svenpetersen1965/C64-PSU-Global/Case/Rev 0/pictures/C64PSU_Global_2020-Feb-03_11-47-49AM-000_CustomizedView1905755716.png

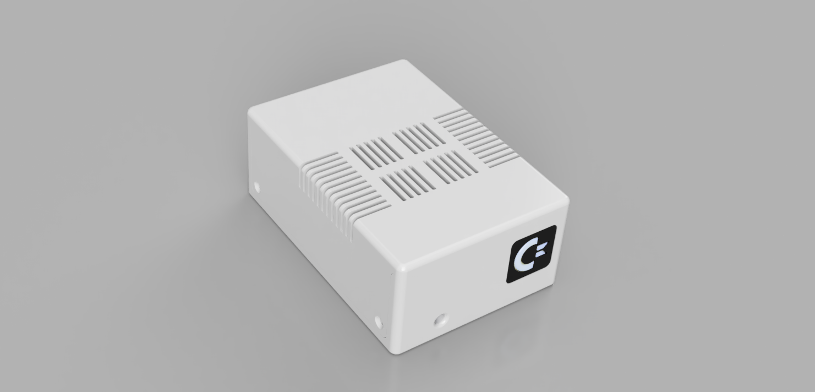
Case/Rev 0/pictures/C64PSU_Global_2020-Feb-03_11-47-49AM-000_CustomizedView1905755716.png
