svenpetersen1965/C64-PSU-Global/Case/Rev 0/pictures/C64PSU_Global_2020-Jan-24_03-44-14PM-000_CustomizedView20103797462.png

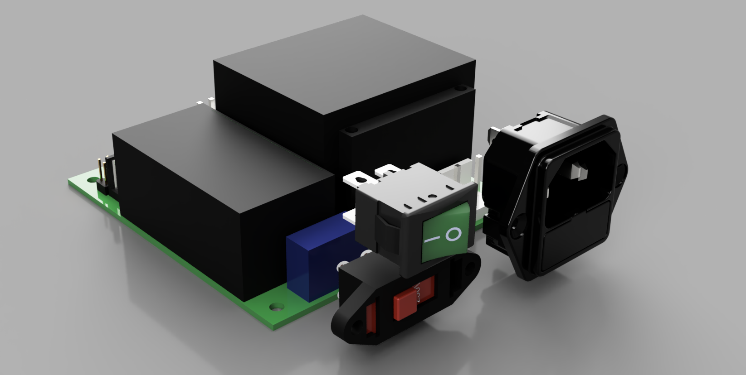
Case/Rev 0/pictures/C64PSU_Global_2020-Jan-24_03-44-14PM-000_CustomizedView20103797462.png
