svenpetersen1965/C64-PSU-Global/Case/Rev 0/pictures/C64PSU_Global_2020-Jan-25_06-23-07PM-000_CustomizedView7411572082.jpg

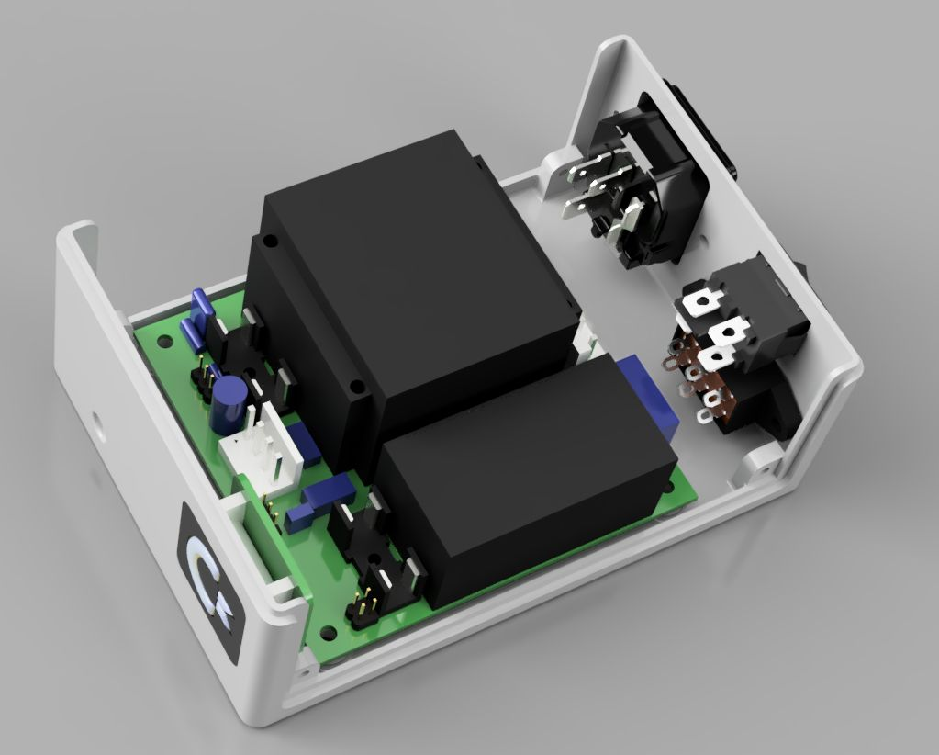
Case/Rev 0/pictures/C64PSU_Global_2020-Jan-25_06-23-07PM-000_CustomizedView7411572082.jpg
