svenpetersen1965/C64-PSU-Global/Case/Rev 0/pictures/C64PSU_Global_2020-Jan-25_08-59-41PM-000_CustomizedView21250095987.jpg

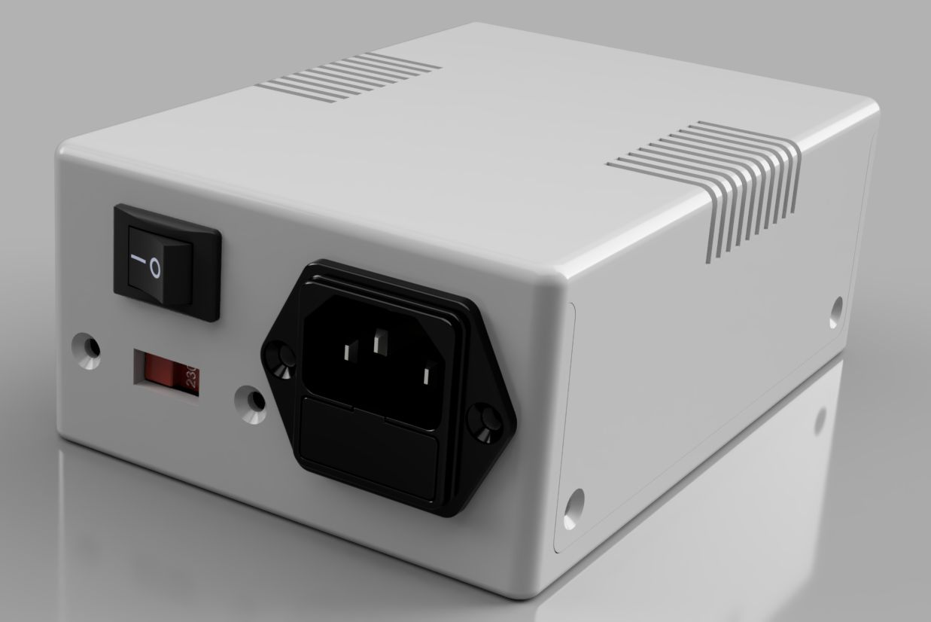
Case/Rev 0/pictures/C64PSU_Global_2020-Jan-25_08-59-41PM-000_CustomizedView21250095987.jpg
