svenpetersen1965/C64-PSU-Global/Case/Rev 0/pictures/C64PSU_Global_2020-Jan-25_12-00-59PM-000_CustomizedView4116816318.jpg

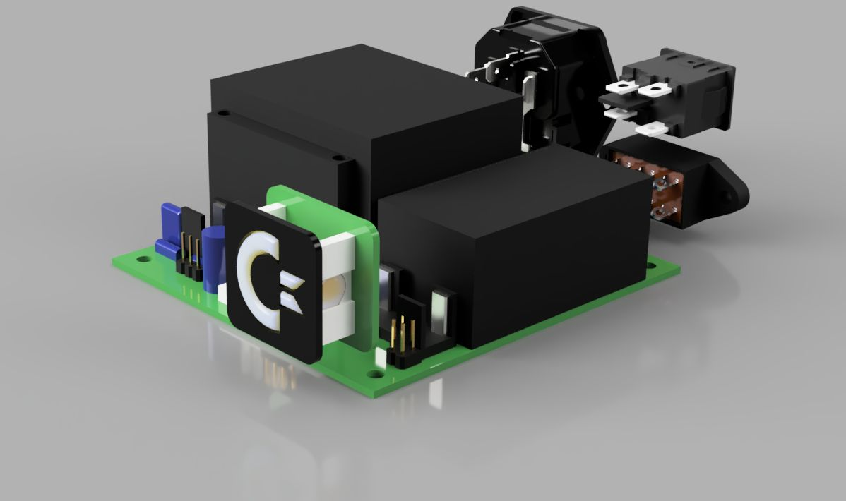
Case/Rev 0/pictures/C64PSU_Global_2020-Jan-25_12-00-59PM-000_CustomizedView4116816318.jpg
