svenpetersen1965/C64-PSU-Global/Rev. 1/Inkscape/C64_PSU_230_115.png

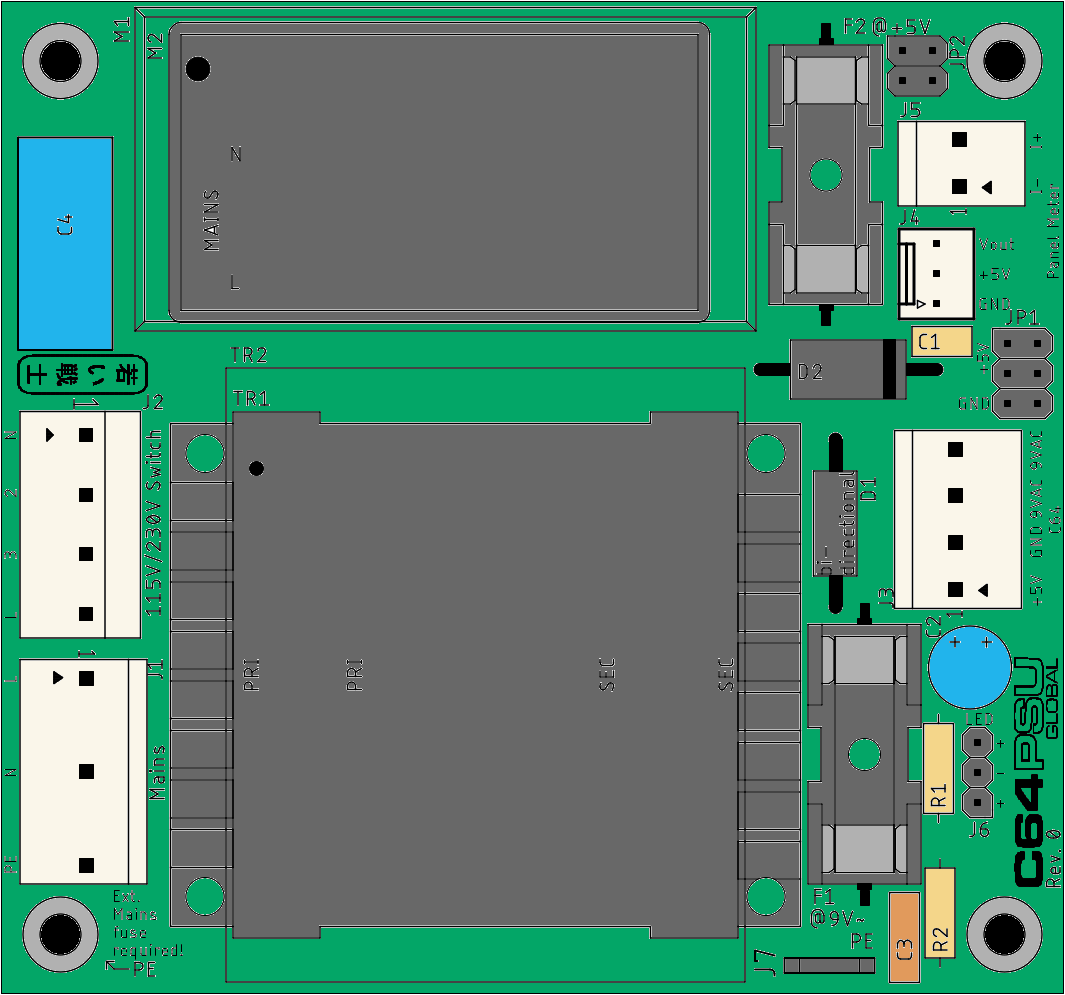
Rev. 1/Inkscape/C64_PSU_230_115.png
