svenpetersen1965/C64-PSU-Global/Rev. 1/pictures/3654_psu_glob_both.JPG

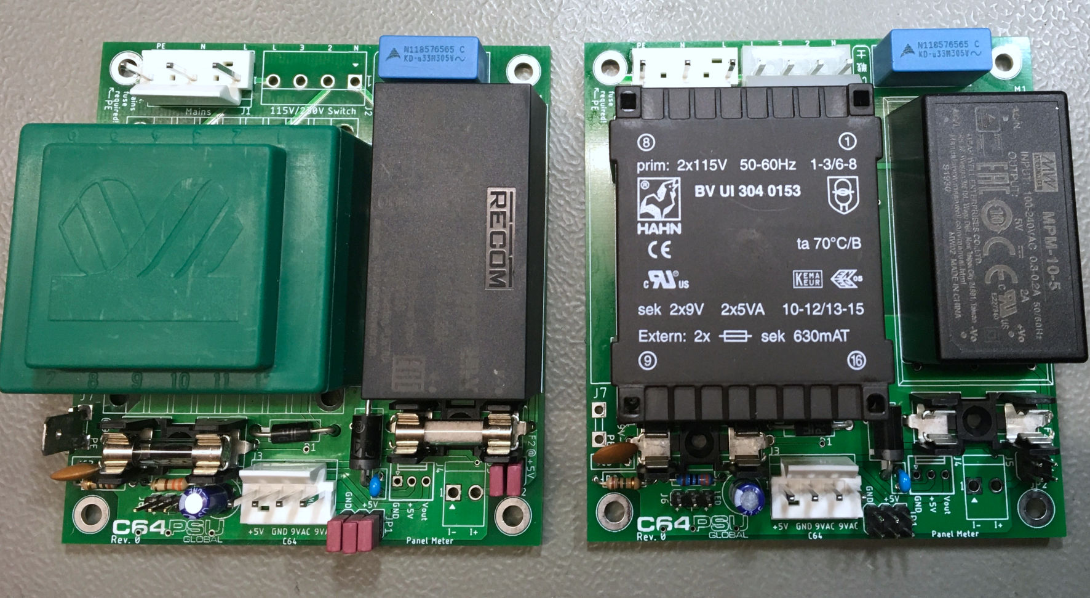
Rev. 1/pictures/3654_psu_glob_both.JPG
