svenpetersen1965/C64-PSU-Global/Rev. 1/pictures/3697_wired_rev0.JPG

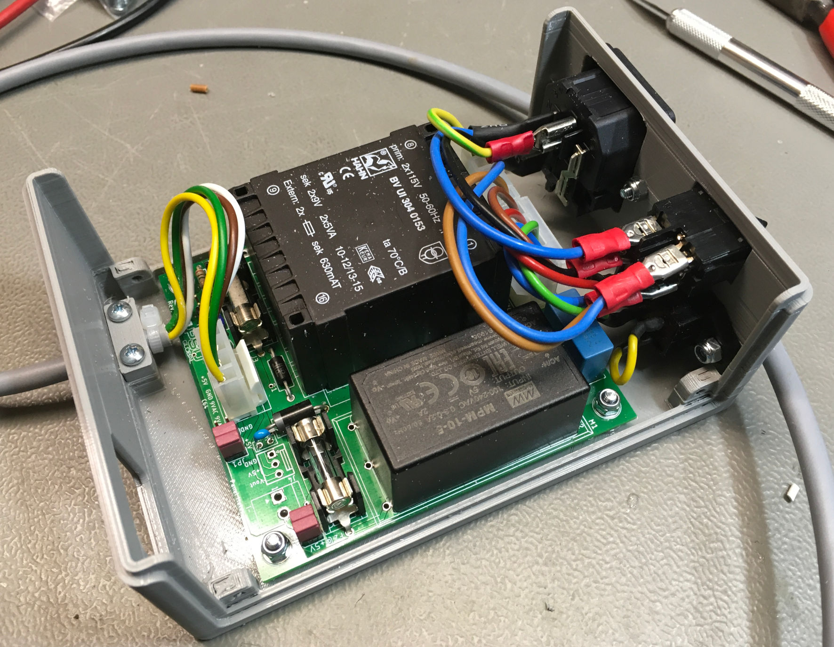
Rev. 1/pictures/3697_wired_rev0.JPG
