svenpetersen1965/C64-PSU-Global/Rev. 1/pictures/3714-mains_cable_inlet.JPG

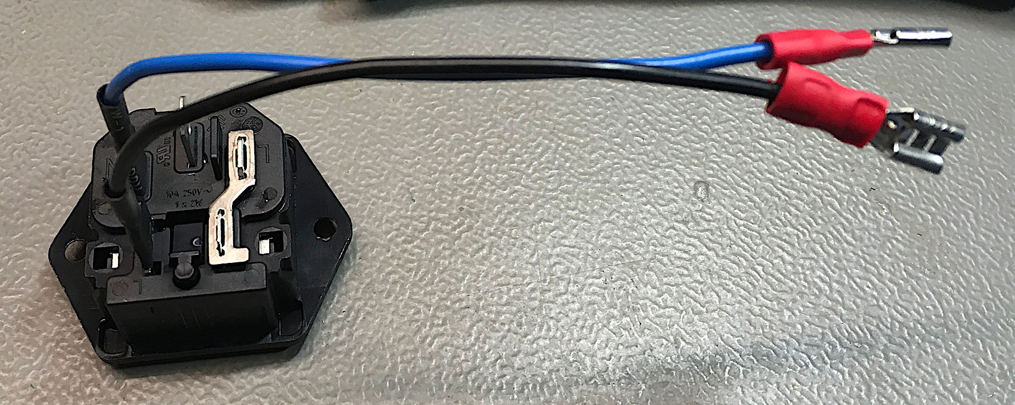
Rev. 1/pictures/3714-mains_cable_inlet.JPG
