svenpetersen1965/C64-PSU-Global/Rev. 1/pictures/3715_appliance_connector_wired.JPG

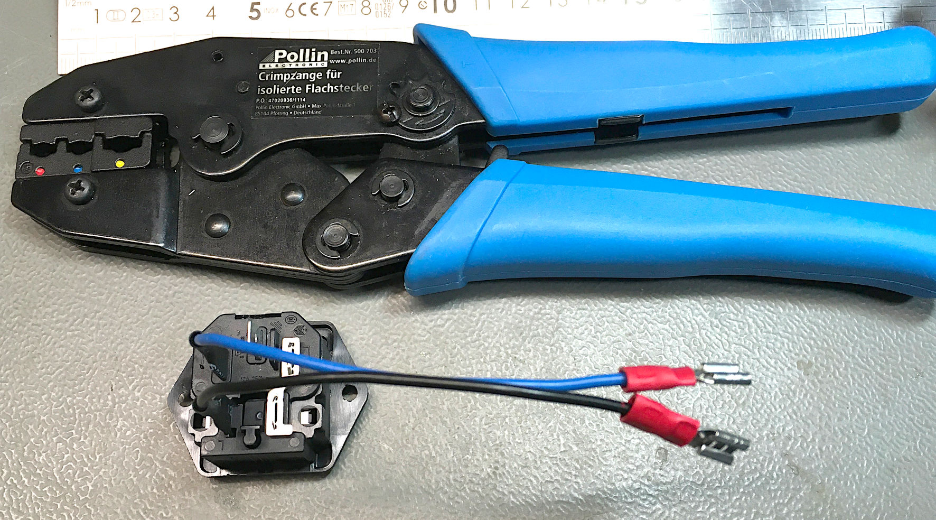
Rev. 1/pictures/3715_appliance_connector_wired.JPG
