svenpetersen1965/C64-PSU-Global/Rev. 1/pictures/3716_power_cable_j1.JPG

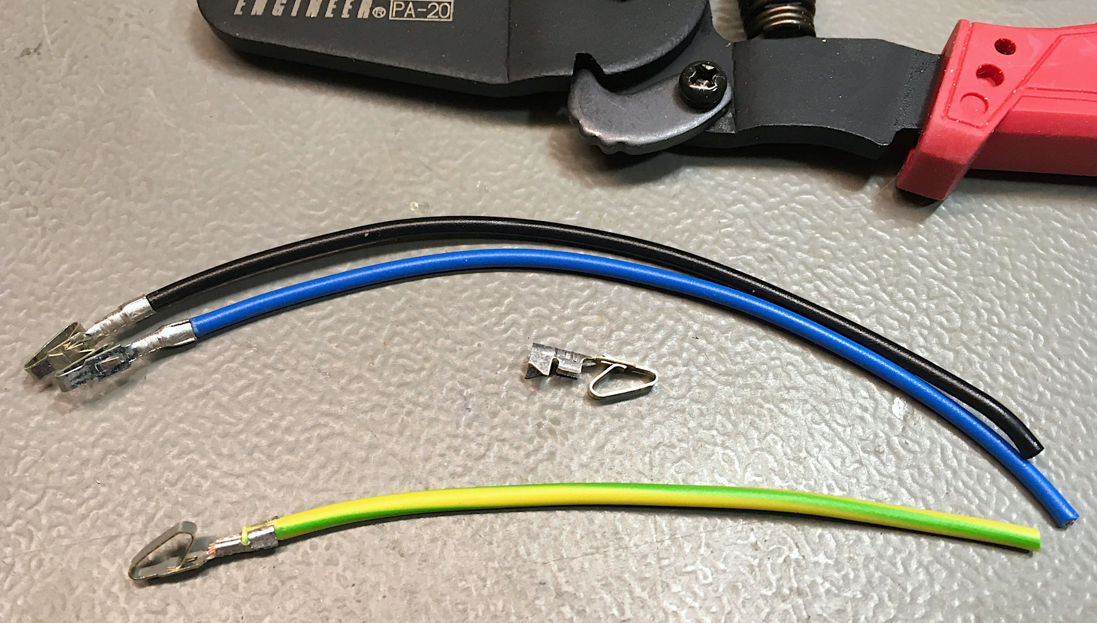
Rev. 1/pictures/3716_power_cable_j1.JPG
