svenpetersen1965/C64-PSU-Global/Rev. 1/pictures/3717_mains_cable.JPG

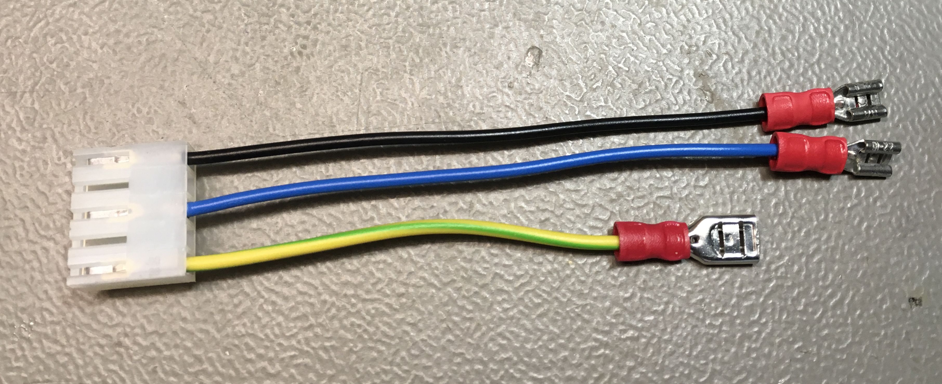
Rev. 1/pictures/3717_mains_cable.JPG
