svenpetersen1965/C64-PSU-Global/Rev. 1/pictures/3718_voltage_selector.JPG

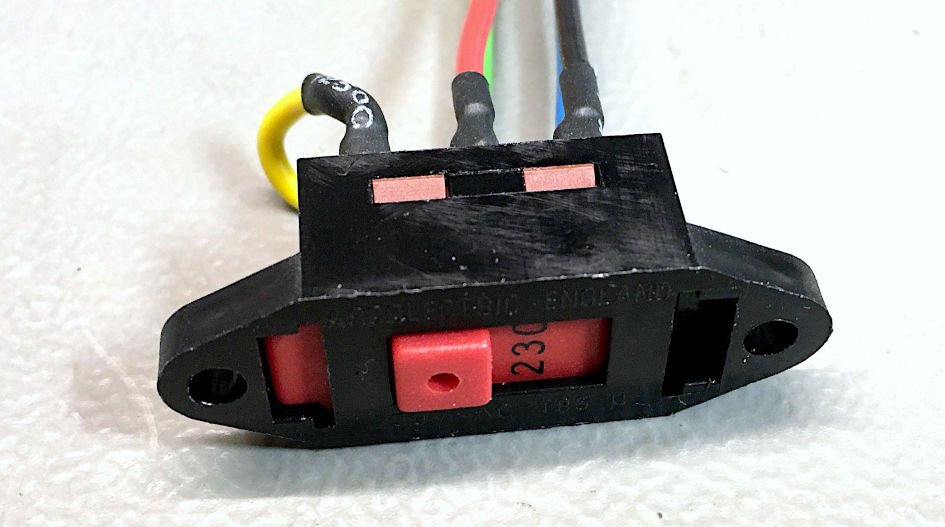
Rev. 1/pictures/3718_voltage_selector.JPG
