svenpetersen1965/C64-PSU-Global/Rev. 1/pictures/3720_voltage_selector_crimped.JPG

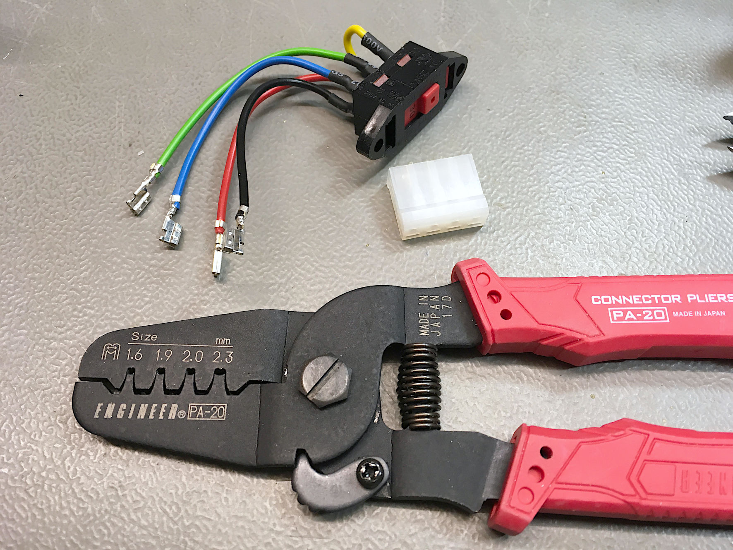
Rev. 1/pictures/3720_voltage_selector_crimped.JPG
