svenpetersen1965/C64-PSU-Global/Rev. 1/pictures/3721_voltage_selector_w300.JPG

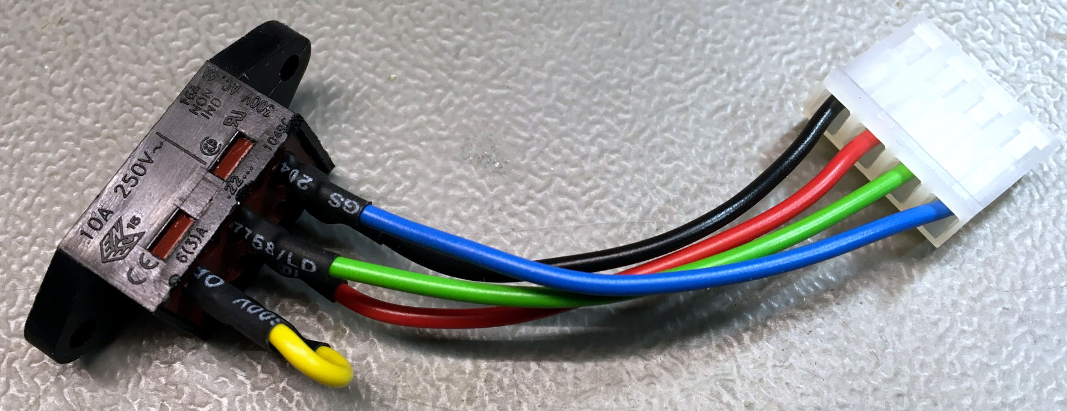
Rev. 1/pictures/3721_voltage_selector_w300.JPG
