svenpetersen1965/C64-PSU-Global/Rev. 1/pictures/3726_mains_switch.JPG

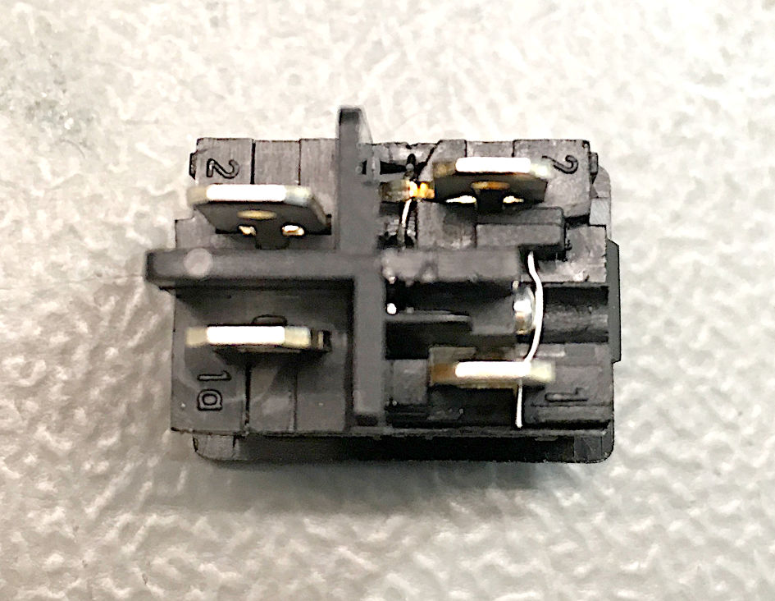
Rev. 1/pictures/3726_mains_switch.JPG
