svenpetersen1965/C64-PSU-Global/Rev. 1/pictures/3728_mains_switch_connected.JPG

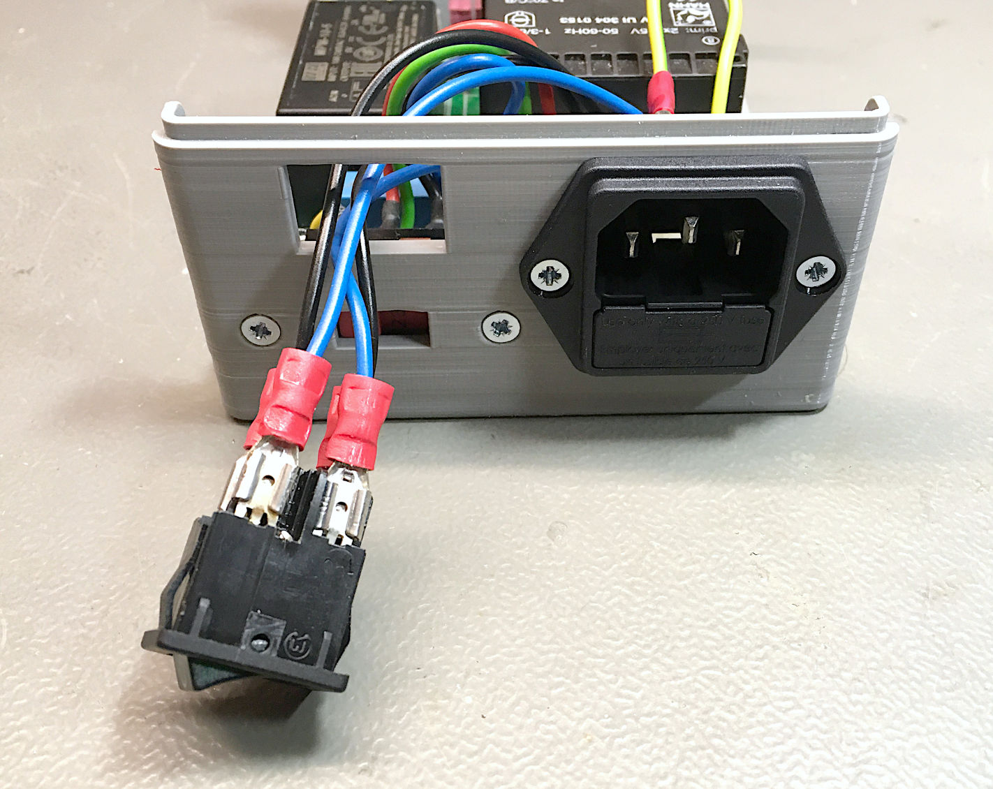
Rev. 1/pictures/3728_mains_switch_connected.JPG
