svenpetersen1965/C64-PSU-Global/Rev. 1/pictures/3742_dim_power_switch_115V.JPG

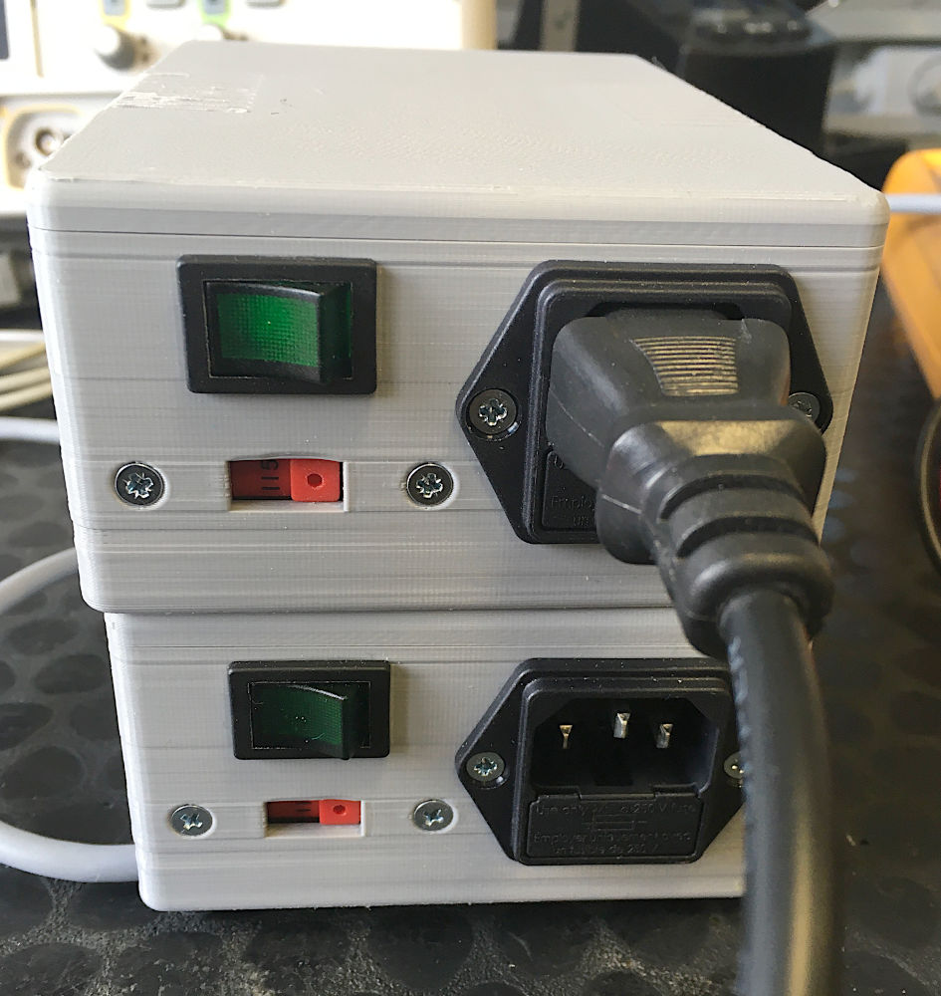
Rev. 1/pictures/3742_dim_power_switch_115V.JPG
