svenpetersen1965/C64-PSU-Global/Rev. 1/pictures/3744_din_connector_output_cable.JPG

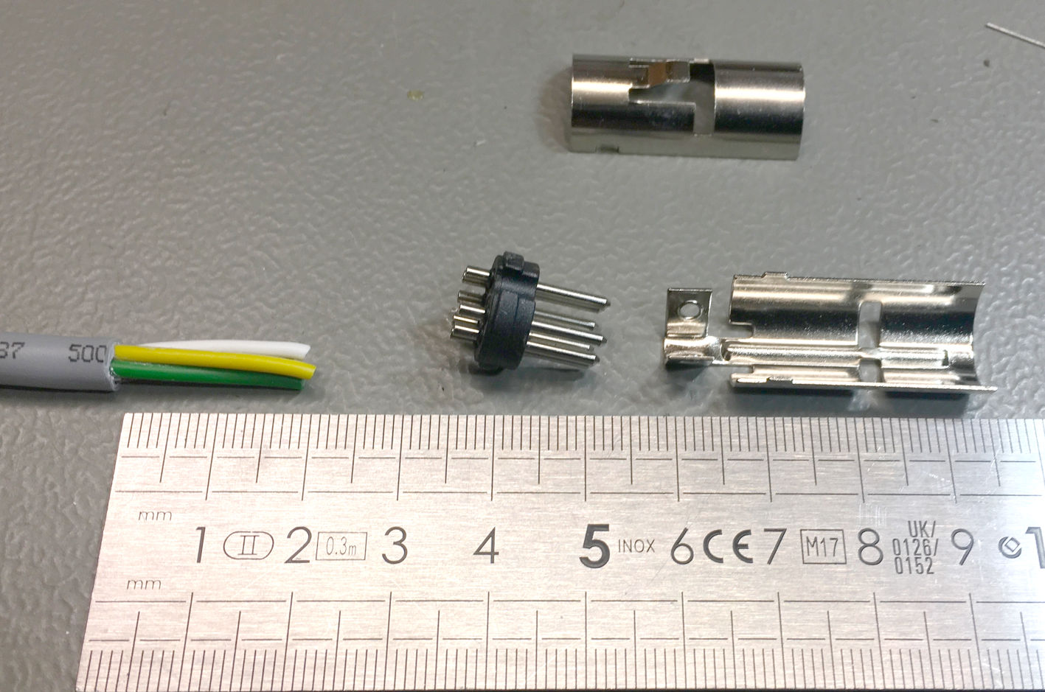
Rev. 1/pictures/3744_din_connector_output_cable.JPG
