svenpetersen1965/C64-PSU-Global/Rev. 1/pictures/3749_din_connector_shield.JPG

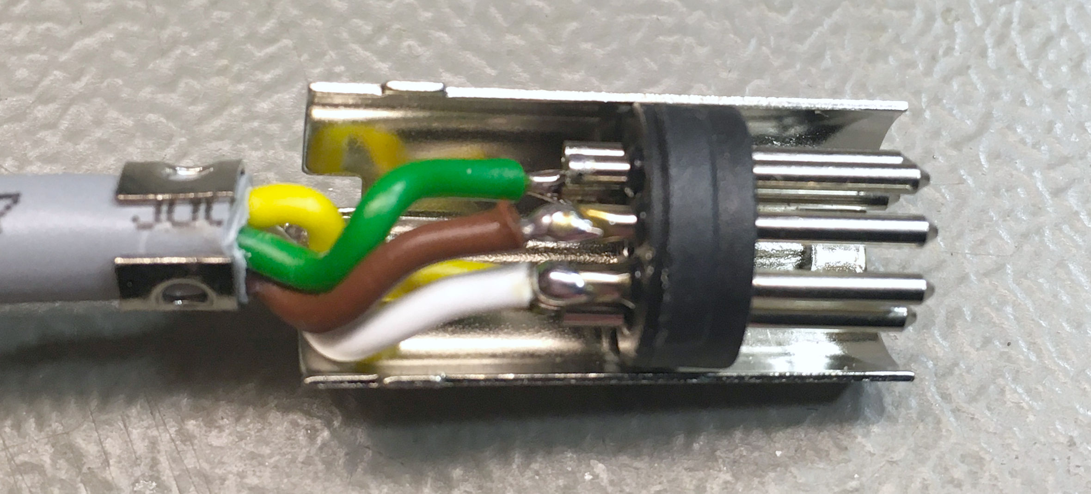
Rev. 1/pictures/3749_din_connector_shield.JPG
