svenpetersen1965/C64-PSU-Global/Rev. 1/pictures/3751_rev0_230V_only.JPG

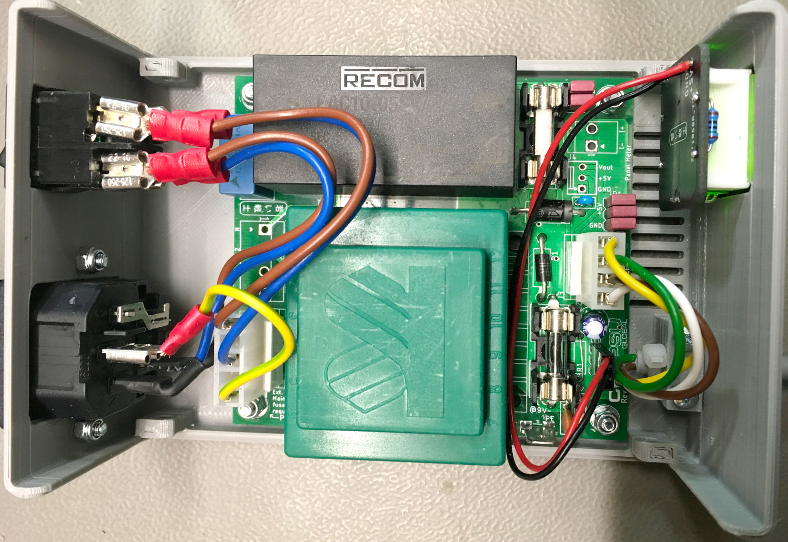
Rev. 1/pictures/3751_rev0_230V_only.JPG
