svenpetersen1965/C64-PSU-Global/Rev. 1/pictures/3837_thermal_resistor_load_initial.JPG

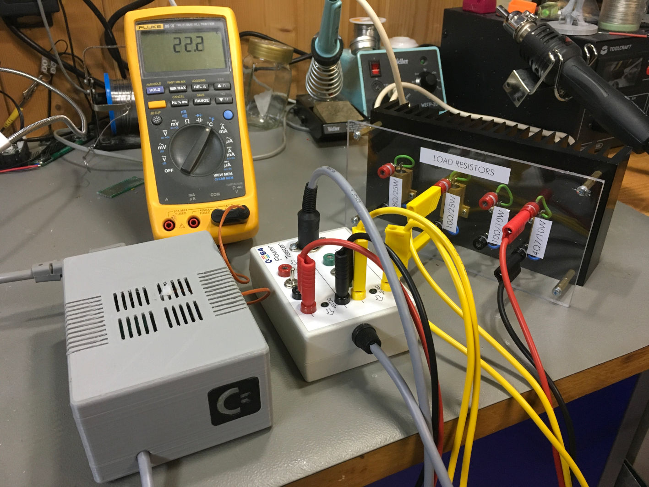
Rev. 1/pictures/3837_thermal_resistor_load_initial.JPG
