svenpetersen1965/C64-PSU-Global/Rev. 1/pictures/3838_thermal_resistor_load_0_28h.JPG

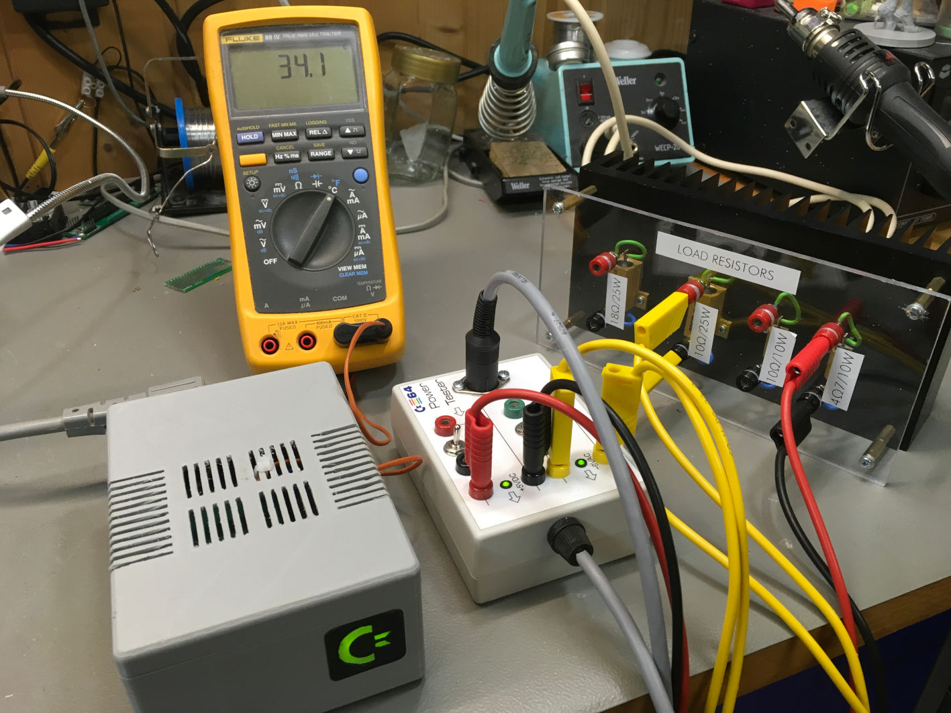
Rev. 1/pictures/3838_thermal_resistor_load_0_28h.JPG
