svenpetersen1965/C64-PSU-Global/Rev. 1/pictures/3839_thermal_resistor_load_02_16h.JPG

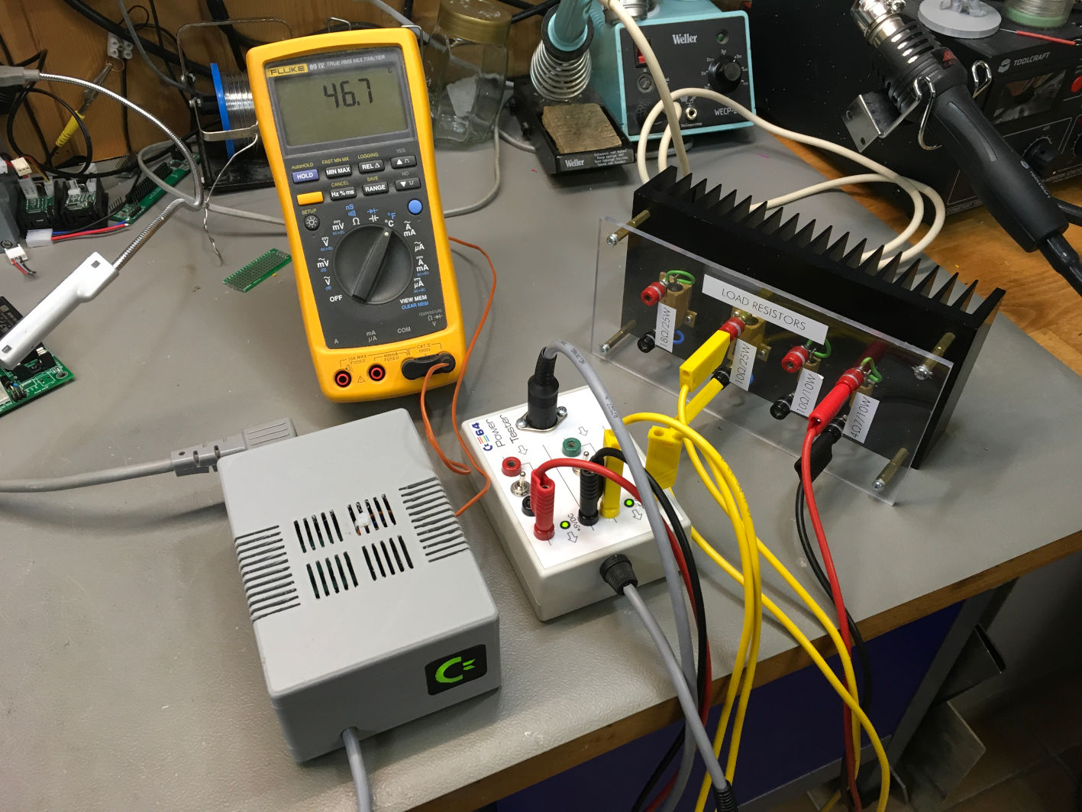
Rev. 1/pictures/3839_thermal_resistor_load_02_16h.JPG
