svenpetersen1965/C64-PSU-Global/Rev. 1/pictures/3840_final_temperature_resistor_load.JPG

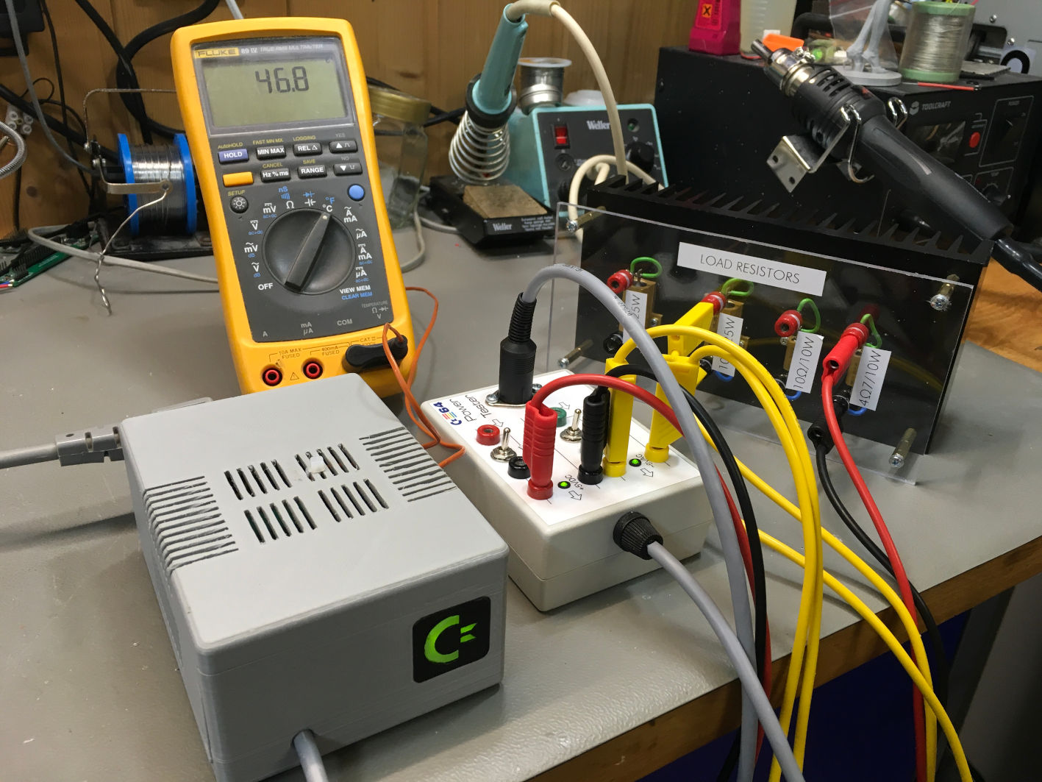
Rev. 1/pictures/3840_final_temperature_resistor_load.JPG
