svenpetersen1965/C64-PSU-Global/Rev. 1/pictures/3842_thermal_RLT_initial.JPG

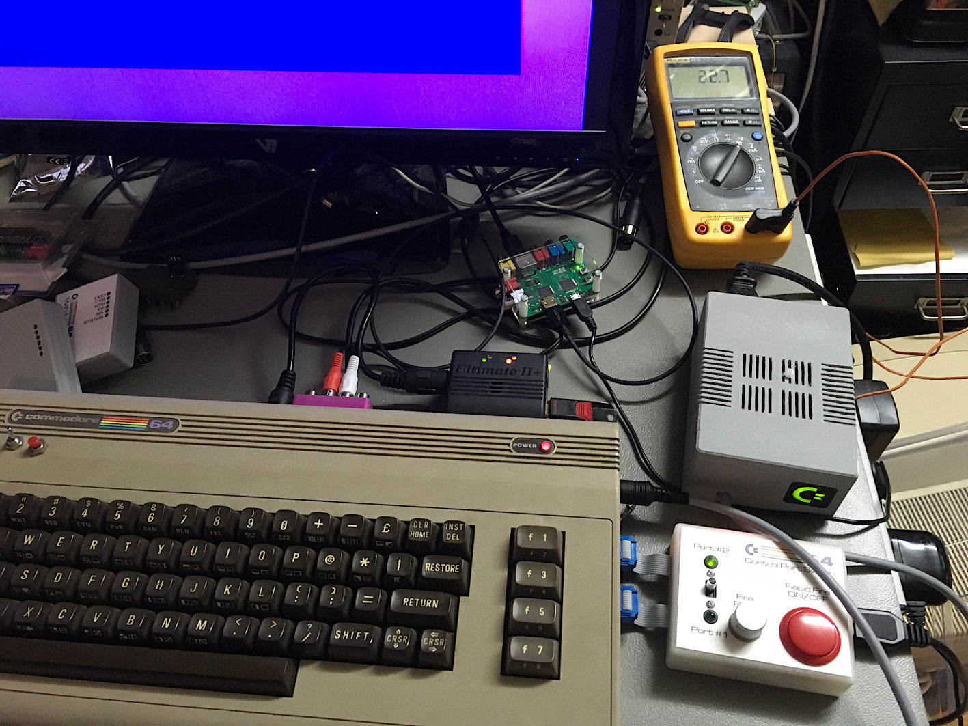
Rev. 1/pictures/3842_thermal_RLT_initial.JPG
