svenpetersen1965/C64-PSU-Global/Rev. 1/pictures/3843_thermal_RLT_0_00h.JPG

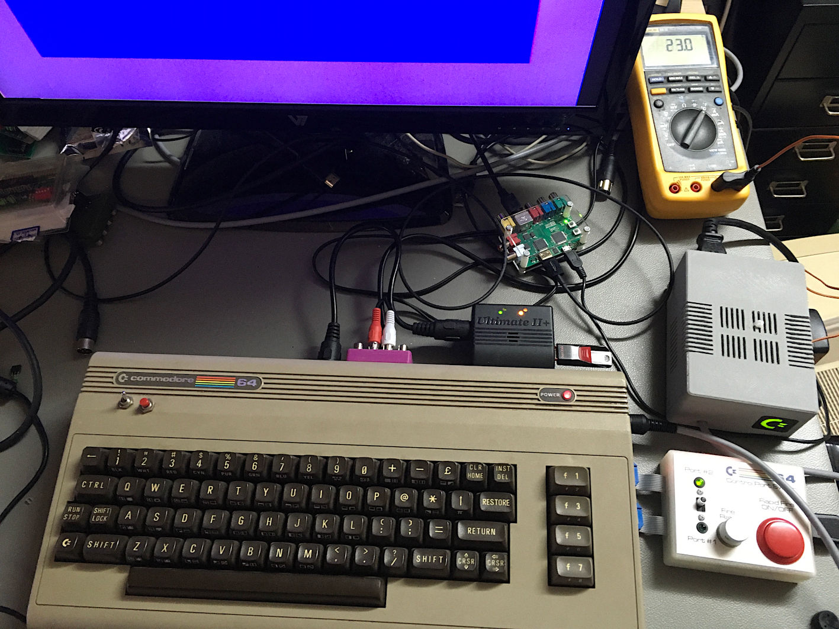
Rev. 1/pictures/3843_thermal_RLT_0_00h.JPG
