svenpetersen1965/C64-PSU-Global/Rev. 1/pictures/3845_thermal_RLT_0_54h.JPG

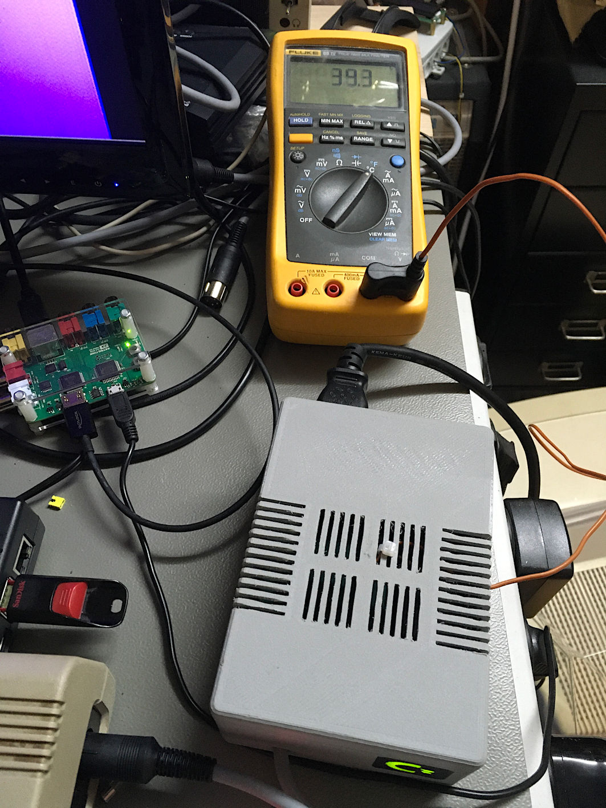
Rev. 1/pictures/3845_thermal_RLT_0_54h.JPG
