svenpetersen1965/C64-PSU-Global/Rev. 1/pictures/3846_thermal_RLT_1_49h.JPG

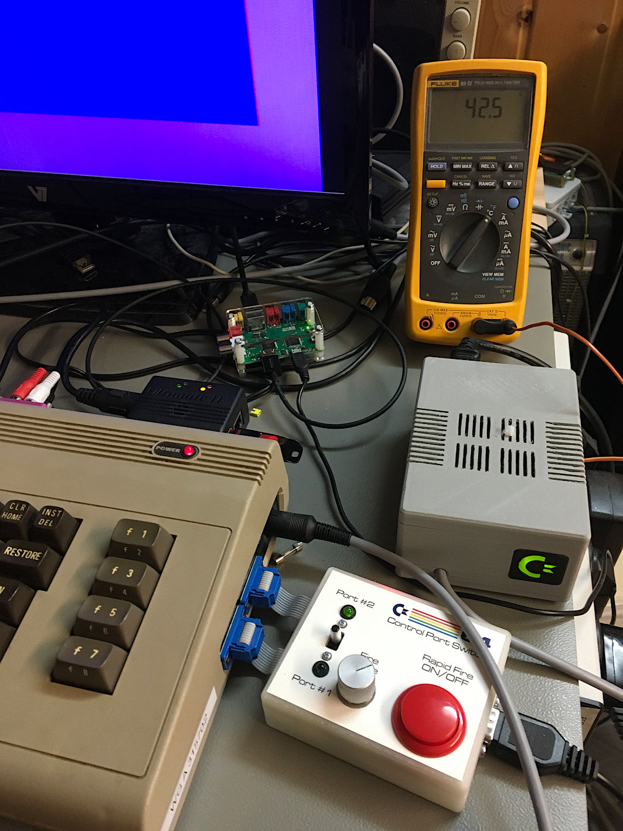
Rev. 1/pictures/3846_thermal_RLT_1_49h.JPG
