svenpetersen1965/C64-PSU-Global/Rev. 1/pictures/3847_thermal_RLT_2_29h.JPG

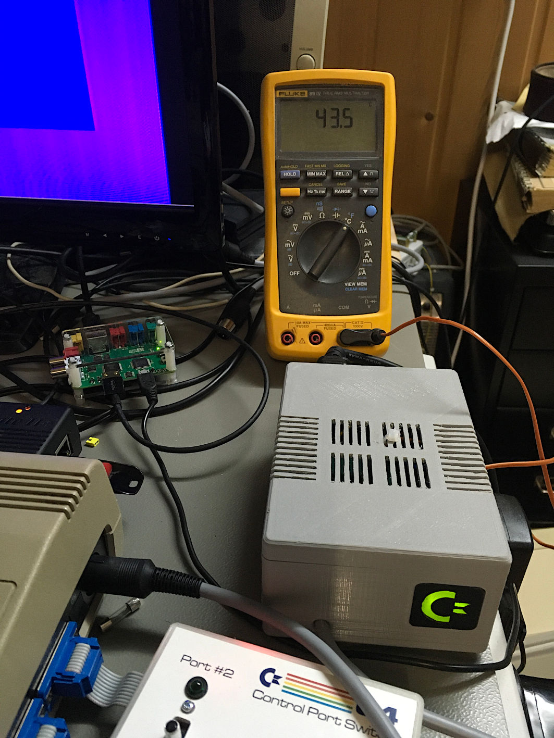
Rev. 1/pictures/3847_thermal_RLT_2_29h.JPG
