svenpetersen1965/C64-PSU-Global/Rev. 1/pictures/4185_c64_PSU_global_Rev_1.JPG

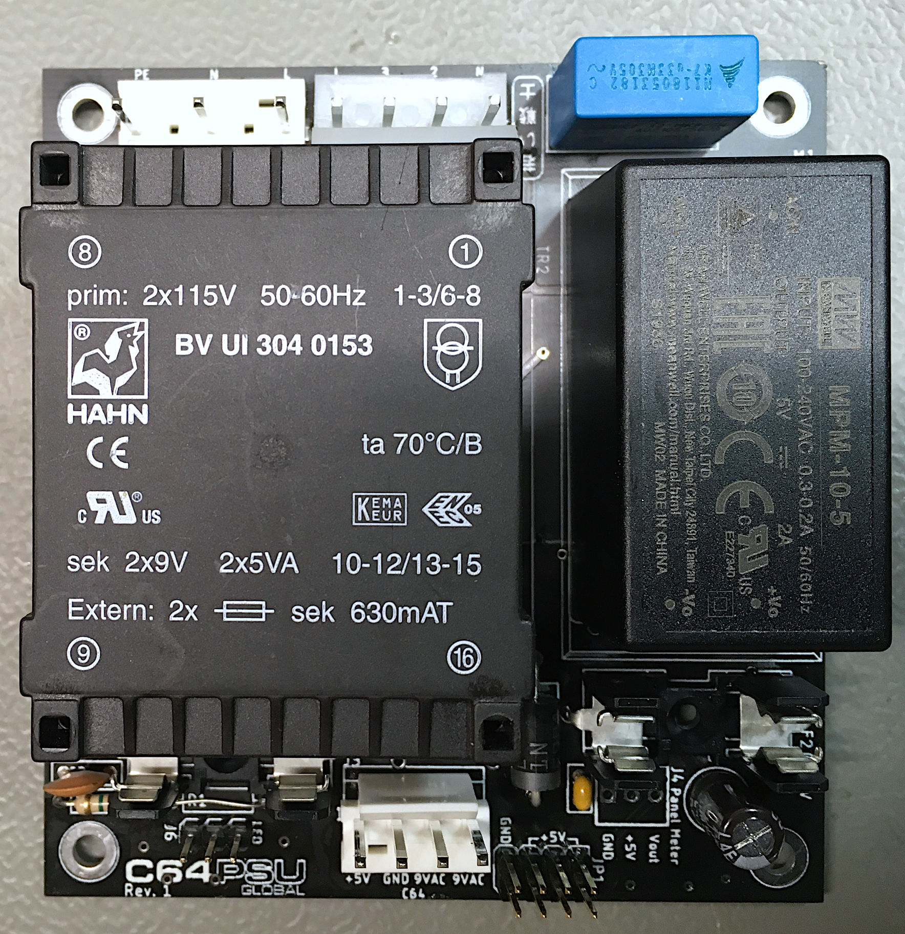
Rev. 1/pictures/4185_c64_PSU_global_Rev_1.JPG
