svenpetersen1965/C64-PSU-Global/Rev. 1/pictures/4326_screws.xnbak.jpg

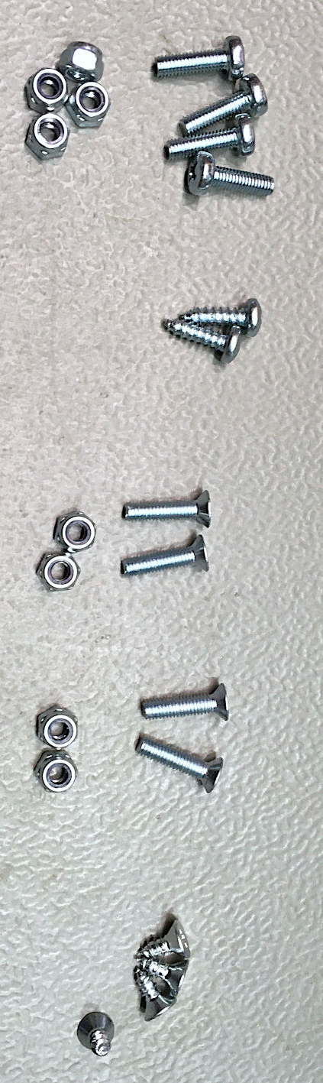
Rev. 1/pictures/4326_screws.xnbak.jpg
