svenpetersen1965/C64-PSU-Global/Rev. 1/pictures/4329_rev1_wired.JPG

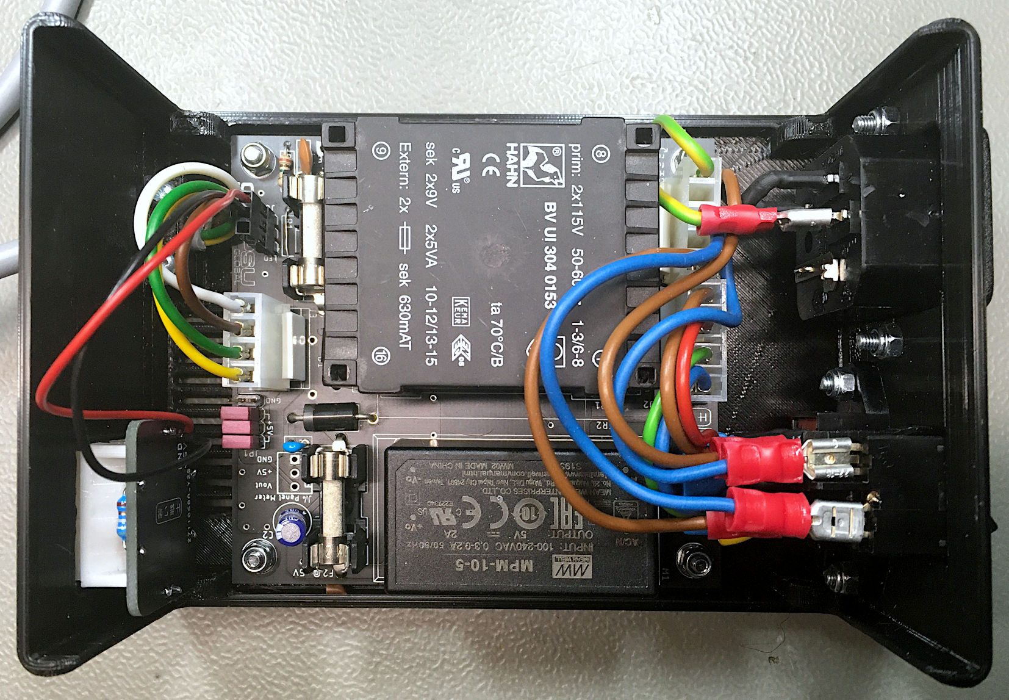
Rev. 1/pictures/4329_rev1_wired.JPG
