svenpetersen1965/C64-PSU-Global/Rev. 1/pictures/block diagram.png

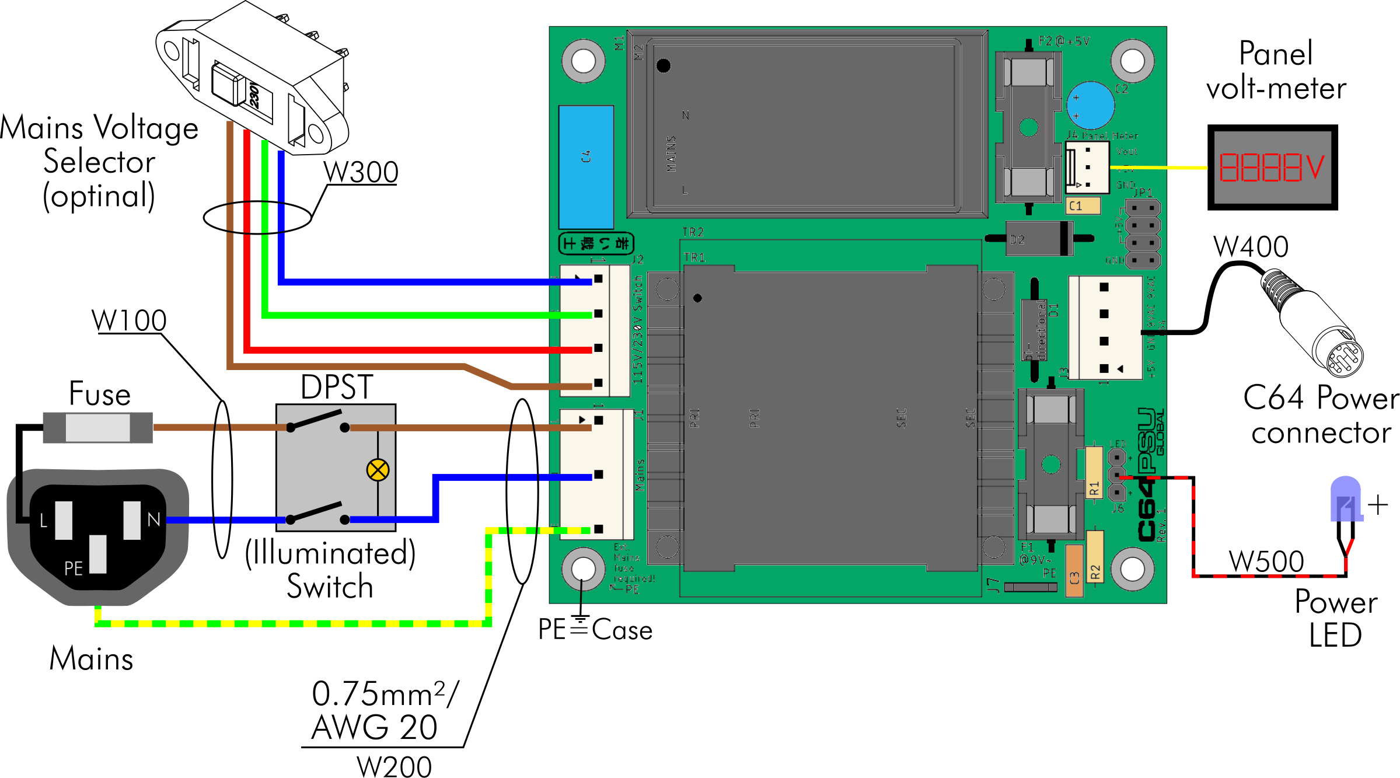
Rev. 1/pictures/block diagram.png
