svenpetersen1965/C64-PSU-Global/Rev. 1/pictures/mains_voltage_selector.png

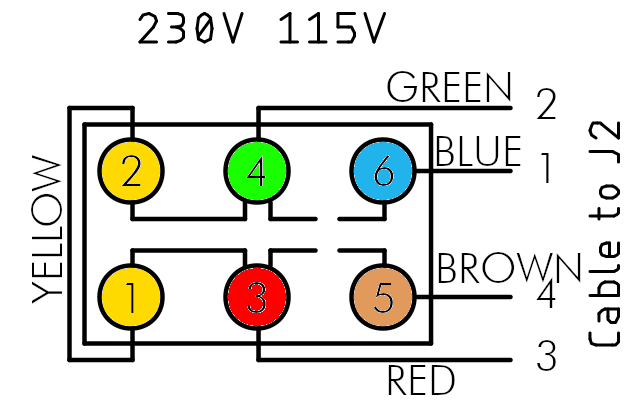
Rev. 1/pictures/mains_voltage_selector.png
