svenpetersen1965/C64-PSU-Global/Rev. 1/pictures/PSU_Global_case_2_bottoms.jpg

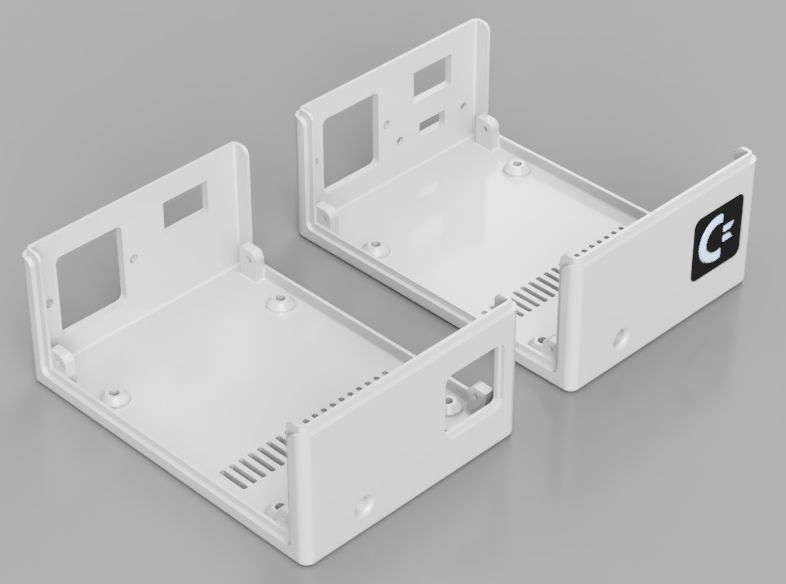
Rev. 1/pictures/PSU_Global_case_2_bottoms.jpg
