svenpetersen1965/C64-PSU-Global/Rev. 1/pictures/3711_installing_output_cable.JPG

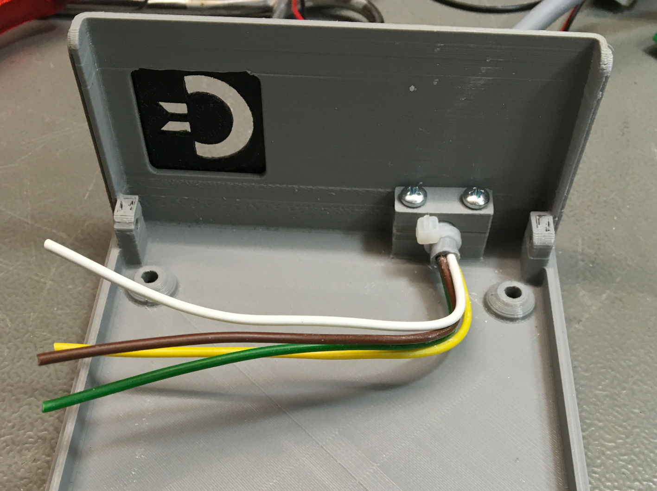
Rev. 1/pictures/3711_installing_output_cable.JPG
