svenpetersen1965/C64-PSU-Global/Rev. 1/pictures/3724_mains_cable_installation.JPG

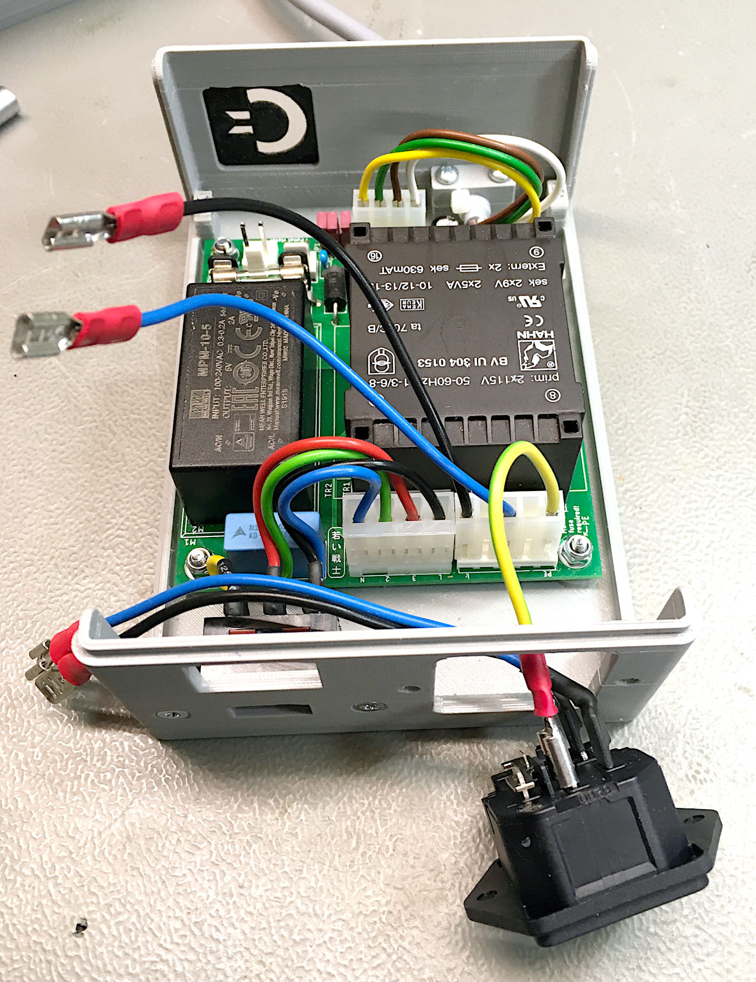
Rev. 1/pictures/3724_mains_cable_installation.JPG
