svenpetersen1965/C64-PSU-Global/Rev. 1/pictures/3727_installing_mains_switch.JPG

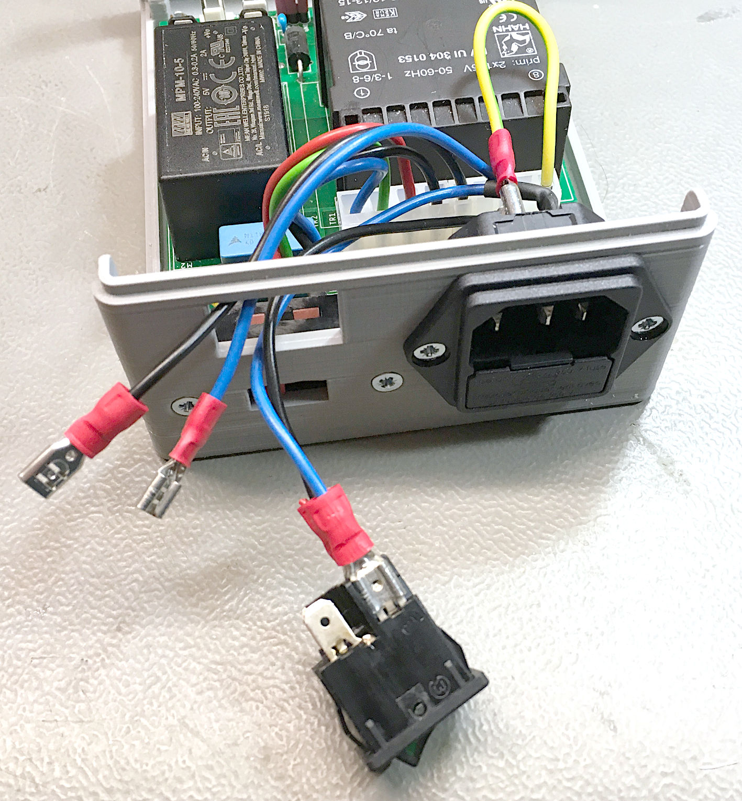
Rev. 1/pictures/3727_installing_mains_switch.JPG
