svenpetersen1965/C64-PSU-Global/Rev. 1/pictures/3729_mains_switch_installed.JPG

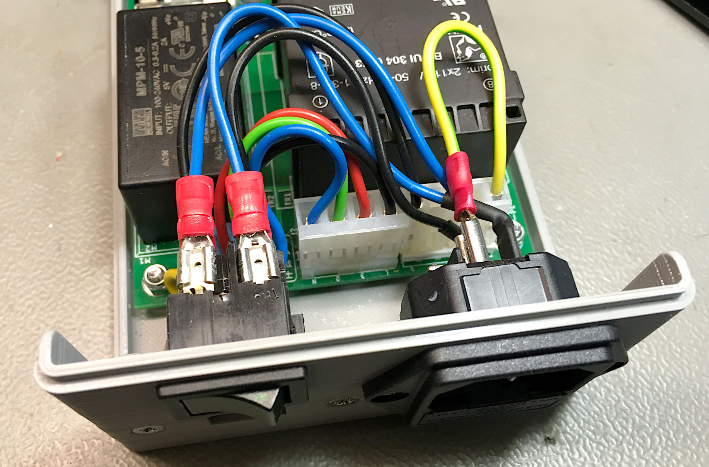
Rev. 1/pictures/3729_mains_switch_installed.JPG
