svenpetersen1965/C64-PSU-Global/Rev. 1/pictures/4206_rev_1_installed.JPG

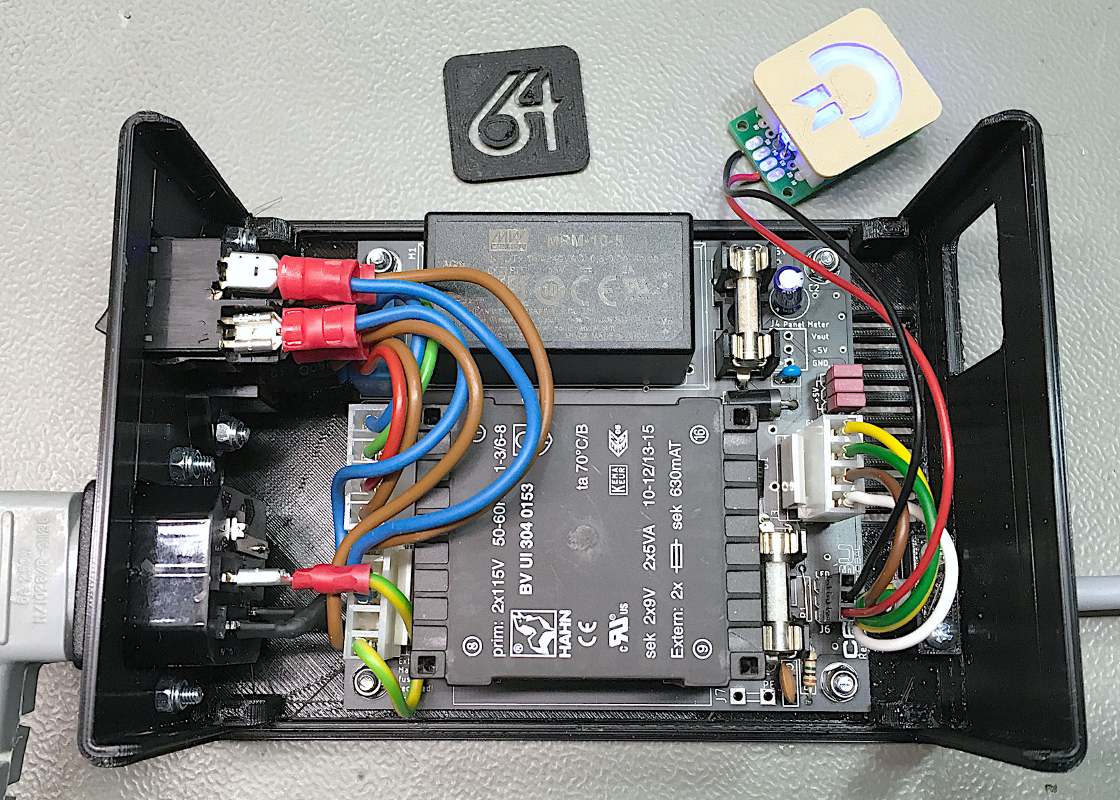
Rev. 1/pictures/4206_rev_1_installed.JPG
