svenpetersen1965/C64-PSU-Global/Rev. 1/pictures/DS4_QuickPrint6.png

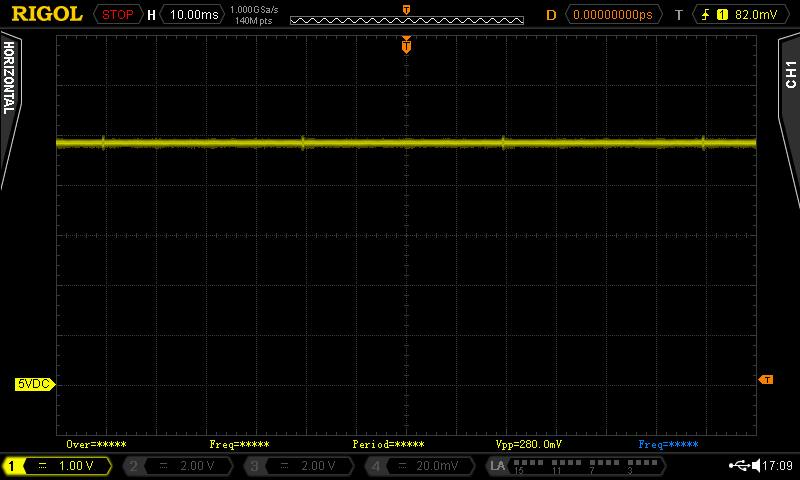
Rev. 1/pictures/DS4_QuickPrint6.png
