svenpetersen1965/C64-PSU-Global/Rev. 1/pictures/DS4_QuickPrint7.png

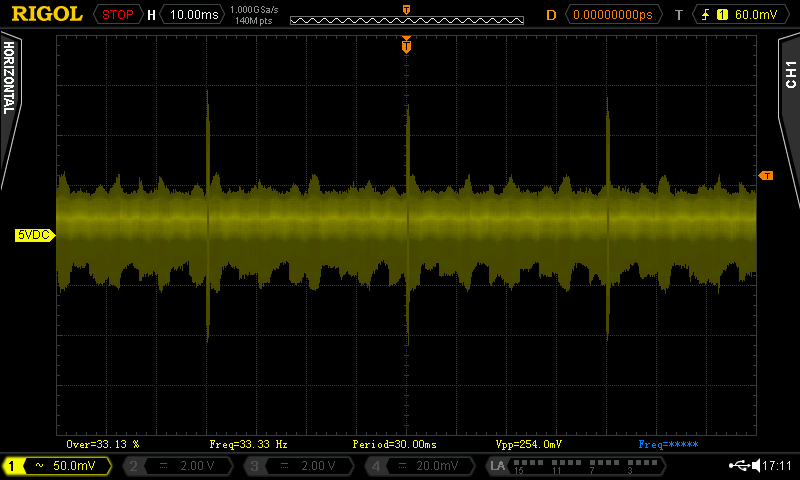
Rev. 1/pictures/DS4_QuickPrint7.png
